blankchenxm/DualStrike/3.Software/Data/calibration/calibration3.csv

counter | sensor_1_x | sensor_1_y | sensor_1_z | sensor_2_x | sensor_2_y | sensor_2_z | sensor_3_x | sensor_3_y | sensor_3_z | sensor_4_x | sensor_4_y | sensor_4_z | sensor_5_x | sensor_5_y | sensor_5_z | sensor_6_x | sensor_6_y | sensor_6_z | sensor_7_x | sensor_7_y | sensor_7_z | sensor_8_x | sensor_8_y | sensor_8_z | timestamp | key_press
0 | -229.20001220703125 | 123.30000305175781 | 202.31199645996094 | -139.65000915527344 | -121.35000610351562 | 371.7120056152344 | 7.650000095367432 | -19.5 | 346.302001953125 | 66.75 | -50.70000076293945 | 387.20001220703125 | -258.75 | 93.45000457763672 | 310.9700012207031 | -69.9000015258789 | 235.8000030517578 | 381.1499938964844 | 19.5 | 324.0 | 366.6300048828125 | 57.30000305175781 | 375.45001220703125 | 406.07598876953125 | 1756211923.4369397 | none
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
