blankchenxm/DualStrike/3.Software/Data/calibration/eavesdrop1.csv

counter | sensor_1_x | sensor_1_y | sensor_1_z | sensor_2_x | sensor_2_y | sensor_2_z | sensor_3_x | sensor_3_y | sensor_3_z | sensor_4_x | sensor_4_y | sensor_4_z | sensor_5_x | sensor_5_y | sensor_5_z | sensor_6_x | sensor_6_y | sensor_6_z | sensor_7_x | sensor_7_y | sensor_7_z | sensor_8_x | sensor_8_y | sensor_8_z | timestamp
2201 | -230.85000610351562 | 121.20000457763672 | 202.31199645996094 | -133.0500030517578 | -132.45001220703125 | 366.14599609375 | -12.0 | -52.20000076293945 | 336.8639831542969 | 74.55000305175781 | -69.9000015258789 | 395.66998291015625 | -262.5 | 98.55000305175781 | 304.6780090332031 | -73.35000610351562 | 216.90000915527344 | 379.94000244140625 | 29.850000381469727 | 291.1500244140625 | 357.1919860839844 | 50.85000228881836 | 353.1000061035156 | 404.8659973144531 | 1755952218.241926
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
