blankchenxm/DualStrike/3.Software/Data/calibration/eavesdrop2.csv

counter | sensor_1_x | sensor_1_y | sensor_1_z | sensor_2_x | sensor_2_y | sensor_2_z | sensor_3_x | sensor_3_y | sensor_3_z | sensor_4_x | sensor_4_y | sensor_4_z | sensor_5_x | sensor_5_y | sensor_5_z | sensor_6_x | sensor_6_y | sensor_6_z | sensor_7_x | sensor_7_y | sensor_7_z | sensor_8_x | sensor_8_y | sensor_8_z | timestamp
822 | -237.75001525878906 | 126.60000610351562 | 205.94200134277344 | -144.15000915527344 | -116.85000610351562 | 371.4700012207031 | 1.9500000476837158 | -28.950000762939453 | 343.39801025390625 | 61.80000305175781 | -55.35000228881836 | 389.6199951171875 | -253.65000915527344 | 101.55000305175781 | 314.6000061035156 | -70.35000610351562 | 233.40000915527344 | 366.87200927734375 | 14.250000953674316 | 324.9000244140625 | 365.90399169921875 | 43.95000076293945 | 372.1500244140625 | 407.04400634765625 | 1756212089.2088692
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
