blankchenxm/DualStrike/3.Software/Data/calibration/eavesdrop3.csv

counter | sensor_1_x | sensor_1_y | sensor_1_z | sensor_2_x | sensor_2_y | sensor_2_z | sensor_3_x | sensor_3_y | sensor_3_z | sensor_4_x | sensor_4_y | sensor_4_z | sensor_5_x | sensor_5_y | sensor_5_z | sensor_6_x | sensor_6_y | sensor_6_z | sensor_7_x | sensor_7_y | sensor_7_z | sensor_8_x | sensor_8_y | sensor_8_z | timestamp
1820 | -234.75001525878906 | 117.9000015258789 | 198.197998046875 | -137.70001220703125 | -116.4000015258789 | 368.3240051269531 | 1.0500000715255737 | -27.750001907348633 | 349.20599365234375 | 66.1500015258789 | -50.70000076293945 | 381.6340026855469 | -253.65000915527344 | 94.35000610351562 | 317.2619934082031 | -71.4000015258789 | 234.90000915527344 | 366.6300048828125 | 16.350000381469727 | 327.9000244140625 | 359.12799072265625 | 56.55000305175781 | 373.20001220703125 | 403.656005859375 | 1756212118.597771
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
