blankchenxm/DualStrike/2.Firmware/DualStrike_Arduino/src/keypress_model_weights.c

#include <stdio.h>
#include <math.h>

#define INPUT_DIM 24
#define HIDDEN_DIM 64
#define OUTPUT_DIM 49

float W1[HIDDEN_DIM][INPUT_DIM] = {
    {0.057931, -0.063160, -0.173795, -0.105394, 0.214797, 0.253317, 0.151077, 0.030987, 0.118751, -0.152882, -0.139365, -0.479122, 0.036581, 0.034106, 0.355291, -0.044247, 0.053712, -0.293586, -0.030915, -0.296490, -0.033501, 0.202679, 0.211489, 0.062248},
    {-0.169693, 0.079964, 0.188349, -0.365637, -0.156665, -0.037280, -0.190257, 0.038901, 0.085432, 0.075148, 0.140170, 0.091890, 0.011354, -0.194503, -0.409434, 0.185256, 0.051886, -0.170961, -0.027169, 0.200173, 0.093718, 0.113058, 0.084636, -0.165012},
    {-0.078226, -0.231870, 0.020550, 0.197172, 0.034525, -0.133433, 0.222992, 0.186662, 0.281546, -0.028478, 0.092414, 0.303362, 0.239206, -0.076183, 0.055459, -0.136498, 0.187880, 0.115121, -0.227378, -0.157221, 0.094687, 0.269169, 0.003302, -0.006740},
    {0.022046, 0.003031, -0.060730, -0.141436, -0.205941, 0.053220, 0.037352, 0.234198, 0.065444, 0.139494, 0.284487, 0.357416, 0.073198, 0.136386, 0.073099, -0.307281, -0.035167, 0.004503, -0.053191, -0.172401, 0.240773, -0.252053, -0.123225, 0.088772},
    {0.123189, -0.178728, -0.073616, -0.306227, 0.164756, -0.063144, 0.375140, -0.022495, -0.079572, 0.302153, -0.005903, 0.144854, -0.061742, -0.128130, 0.150957, 0.252609, -0.127291, -0.190803, 0.286991, -0.145933, -0.104068, -0.302383, 0.014433, 0.006692},
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
};

float b2[OUTPUT_DIM] = {-0.046206, 0.116981, 0.190852, -0.319395, 0.100225, -0.066874, -0.083403, 0.055094, 0.051337, -0.056012, 0.048240, -0.188889, -0.286707, 0.051545, -0.095351, -0.240318, -0.161921, 0.235529, -0.117472, -0.080087, -0.255729, 0.125609, -0.062248, -0.084040, -0.014766, -0.296991, -0.048925, -0.078710, 0.125209, -0.007805, 0.175029, -0.083572, 0.083203, -0.345722, -0.231777, 0.261538, -0.033653, 0.013102, -0.049212, 0.008749, -0.364725, 0.259152, 0.245813, 0.174373, 0.054399, 0.120114, -0.120619, 0.047154, 0.178762};
